AndyTakker/Freshener_ch32/Electronics/Freshener_ch32/Freshener_ch32.kicad_sch

## KiCad design Electronics/Freshener_ch32/Freshener_ch32.kicad_sch (2026-02-08)

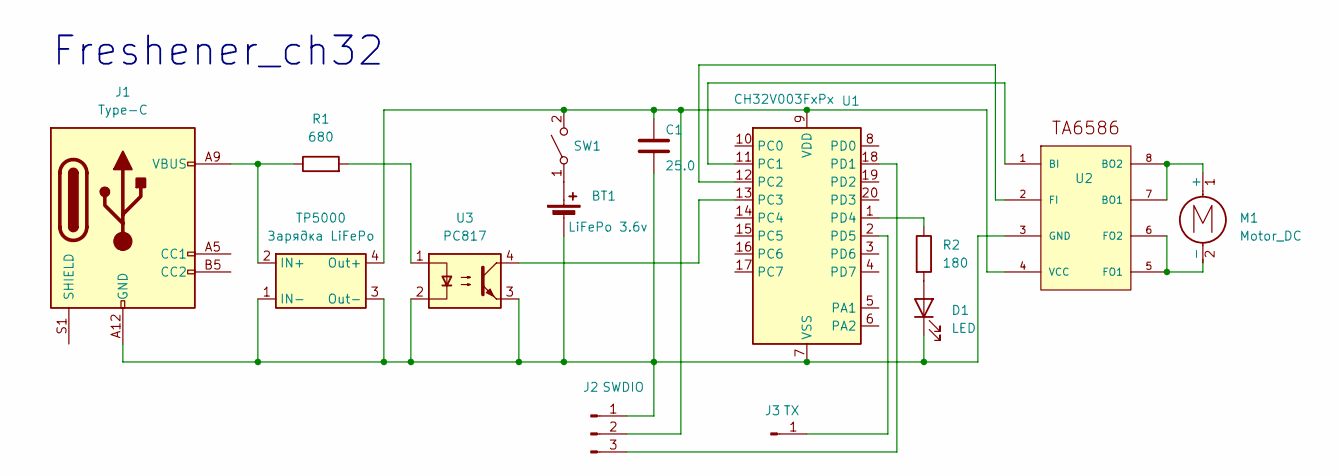
[picture p2: schematic Freshener_ch32.kicad_sch]

Parts:
BT1: LiFePo 3.6v
C1: 25.0
D1: LED
J1: Type-C
J2: SWDIO
J3: TX
M1: Motor_DC
R1: 680
R2: 180
SW1: SW_SPST
TP5000: Зарядка LiFePo
U1: CH32V003FxPx; TSSOP-20_4.4x6.5mm_P0.65mm
U2: TA6586; TA6586-DIP8
U3: PC817; DIP-4_W7.62mm

Connections:
unnamed: BT1.1 (+), SW1.1 (A)
unnamed: BT1.2 (-), C1.2, D1.1 (K), J1.A12 (GND), J1.B12 (GND), J2.1, TP5000.1 (IN-), TP5000.3 (Out-), U1.7 (VSS), U2.3 (GND), U3.2, U3.3
unnamed: C1.1, J2.2, SW1.2 (B), TP5000.4 (Out+), U1.9 (VDD), U2.4 (VCC)
unnamed: D1.2 (A), R2.2
unnamed: J1.A9 (VBUS), J1.B9 (VBUS), R1.1, TP5000.2 (IN+)
unnamed: J2.3, U1.18 (PD1)
unnamed: J3.1, U1.2 (PD5)
unnamed: M1.1 (+), U2.7 (BO1), U2.8 (BO2)
unnamed: M1.2 (-), U2.5 (FO1), U2.6 (FO2)
unnamed: R1.2, U3.1
unnamed: R2.1, U1.1 (PD4)
unnamed: U1.11 (PC1), U2.1 (BI)
unnamed: U1.12 (PC2), U2.2 (FI)
unnamed: U1.13 (PC3), U3.4

Notes on the sheet:
Freshener_ch32
